akakikuumeri/Akaki-Joystick/hinge cam slider for ver C.stl

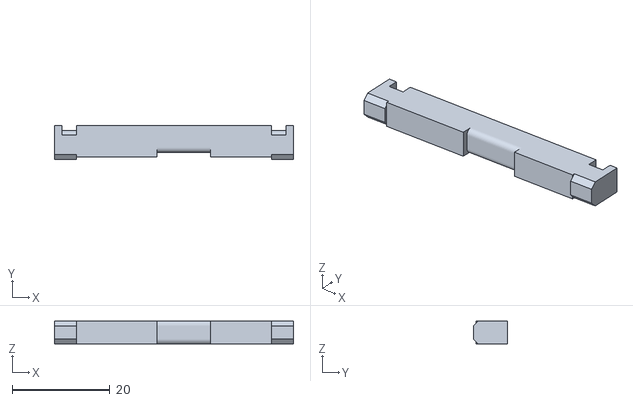
[picture p15: CAD file, 2020-09-15]
hinge cam slider for ver C.stl
49.0 x 7.00 x 4.70
