akakikuumeri/Akaki-Joystick/joystick grip face buttons mount plate.stl

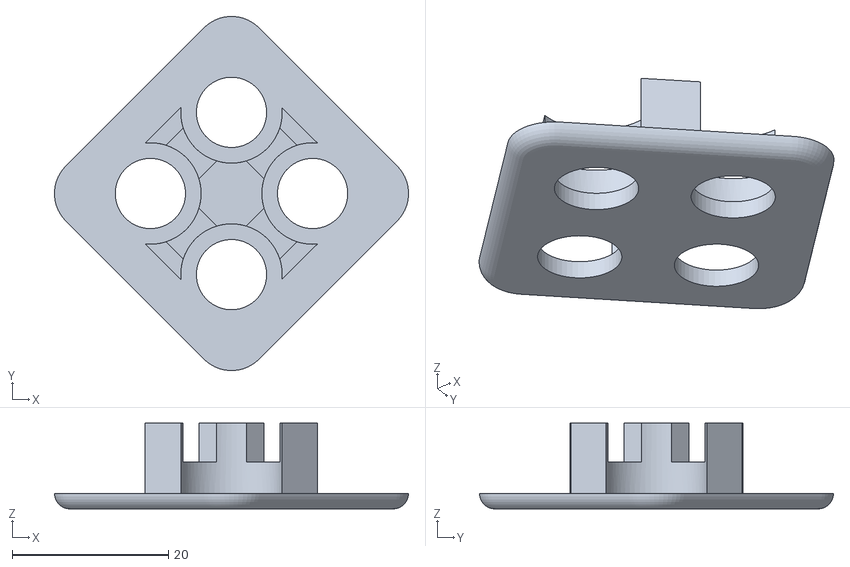
[picture p16: CAD file, 2020-09-15]
joystick grip face buttons mount plate.stl
45.3 x 45.3 x 11.0
