akakikuumeri/Akaki-Joystick/trim knob.stl

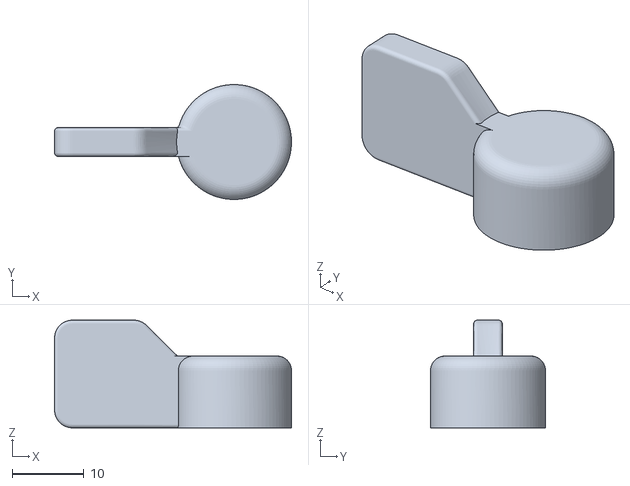
[picture p17: CAD file, 2020-09-15]
trim knob.stl
33.0 x 16.0 x 15.0
