akakikuumeri/Akaki-Joystick/joystick grip right side.stl

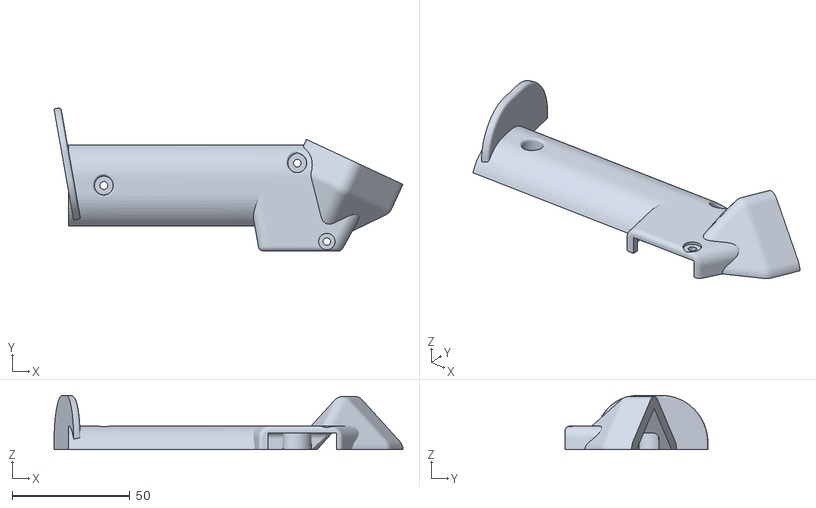
[picture p18: CAD file, 2020-09-15]
joystick grip right side.stl
148.5 x 60.8 x 23.0
